blueflame1929/Mini-PCIe-Kineis-KIM1/Hardware/PCB/IMP-00008-X01-EC-TOP-IL1.pdf

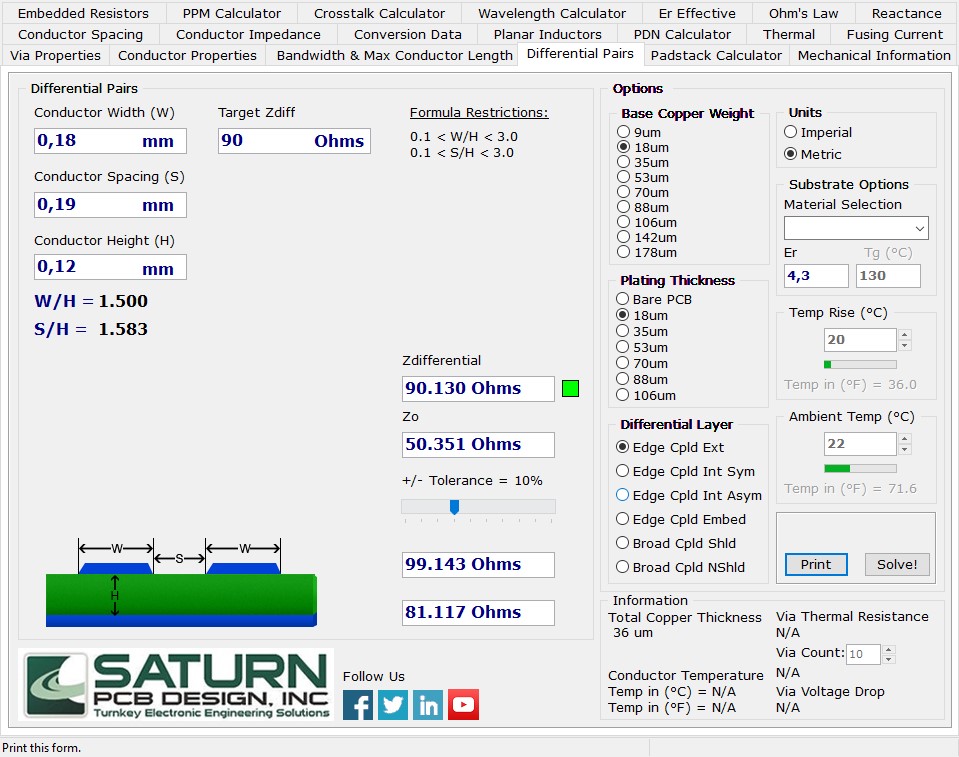
[picture p3: page 1]
