blueflame1929/Mini-PCIe-Kineis-KIM1/Hardware/PCB/IMP-00008-X01-MS-TOP-IL1.pdf

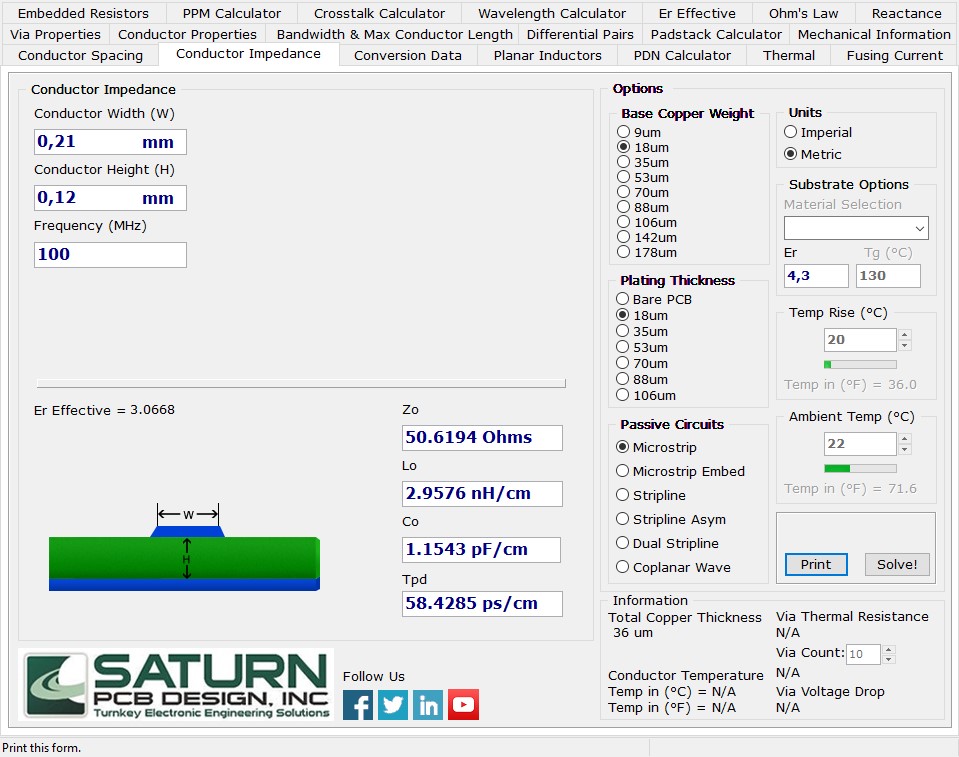
[picture p4: page 1]
