blueflame1929/Mini-PCIe-Kineis-KIM1/Hardware/ASY/B3D-00008-X01.png

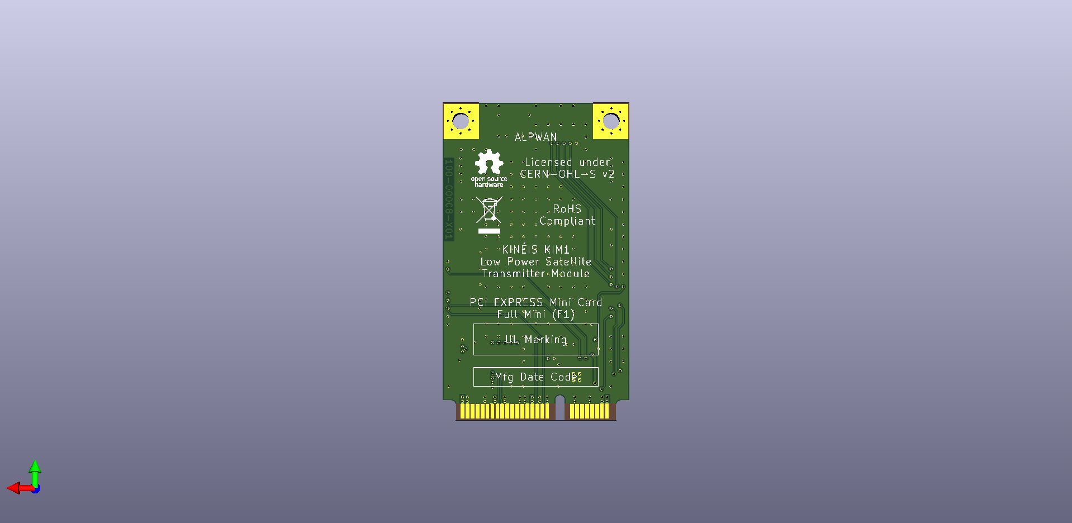
Hardware/ASY/B3D-00008-X01.png
