blueflame1929/Mini-PCIe-Kineis-KIM1/Hardware/PCB/MDD-00008-X01.pdf

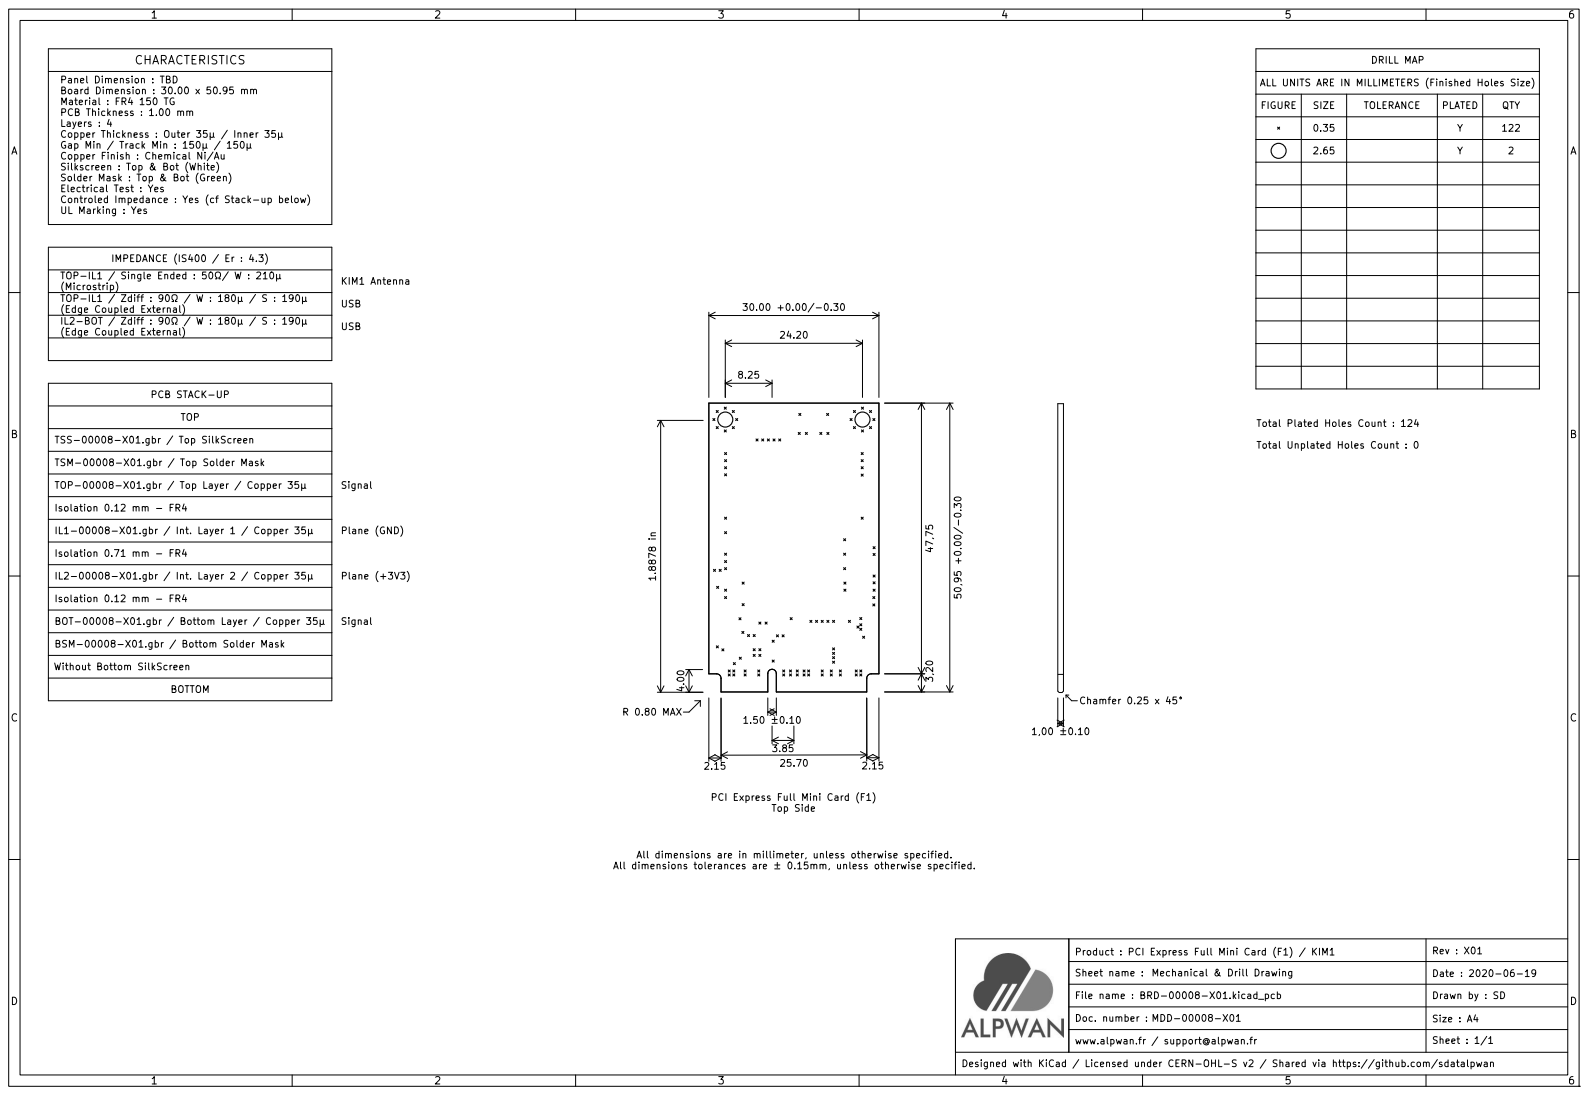
[picture p7: page 1]

IMPEDANCE (IS400 / Er : 4.3) Panel Dimension : TBD
Board Dimension : 30.00 x 50.95 mm
Material : FR4 150 TG
PCB Thickness : 1.00 mm
Layers : 4 Copper Thickness : Outer 35µ / Inner 35µ Gap Min / Track Min : 150µ / 150µ Copper Finish : Chemical Ni/Au Silkscreen : Top & Bot (White) Solder Mask : Top & Bot (Green) Electrical Test : Yes Controled Impedance : Yes (cf Stack-up below) UL Marking : Yes

TOP-IL1 / Single Ended : 50/ W : 210µ
Signal KIM1 Antenna USB TOP-IL1 / Zdiff : 90 / W : 180µ / S : 190µ

IL1-00008-X01.gbr / Int. Layer 1 / Copper 35µ PCB STACK-UP BSM-00008-X01.gbr / Bottom Solder Mask TOP

Isolation 0.12 mm - FR4 TSS-00008-X01.gbr / Top SilkScreen

Isolation 0.71 mm - FR4 TSM-00008-X01.gbr / Top Solder Mask

TOP-00008-X01.gbr / Top Layer / Copper 35µ Without Bottom SilkScreen

IL2-00008-X01.gbr / Int. Layer 2 / Copper 35µ

BOT-00008-X01.gbr / Bottom Layer / Copper 35µ

Rev : X01 Size : A4 Sheet : 1/1 Product : PCI Express Full Mini Card (F1) / KIM1 Sheet name : All dimensions are in millimeter, unless otherwise specified. All dimensions tolerances are ± 0.15mm, unless otherwise specified. PCI Express Full Mini Card (F1) Top Side

MDD-00008-X01 Mechanical & Drill Drawing
