blueflame1929/Mini-PCIe-Kineis-KIM1/Hardware/SCH/SCH-00008-X01.pdf

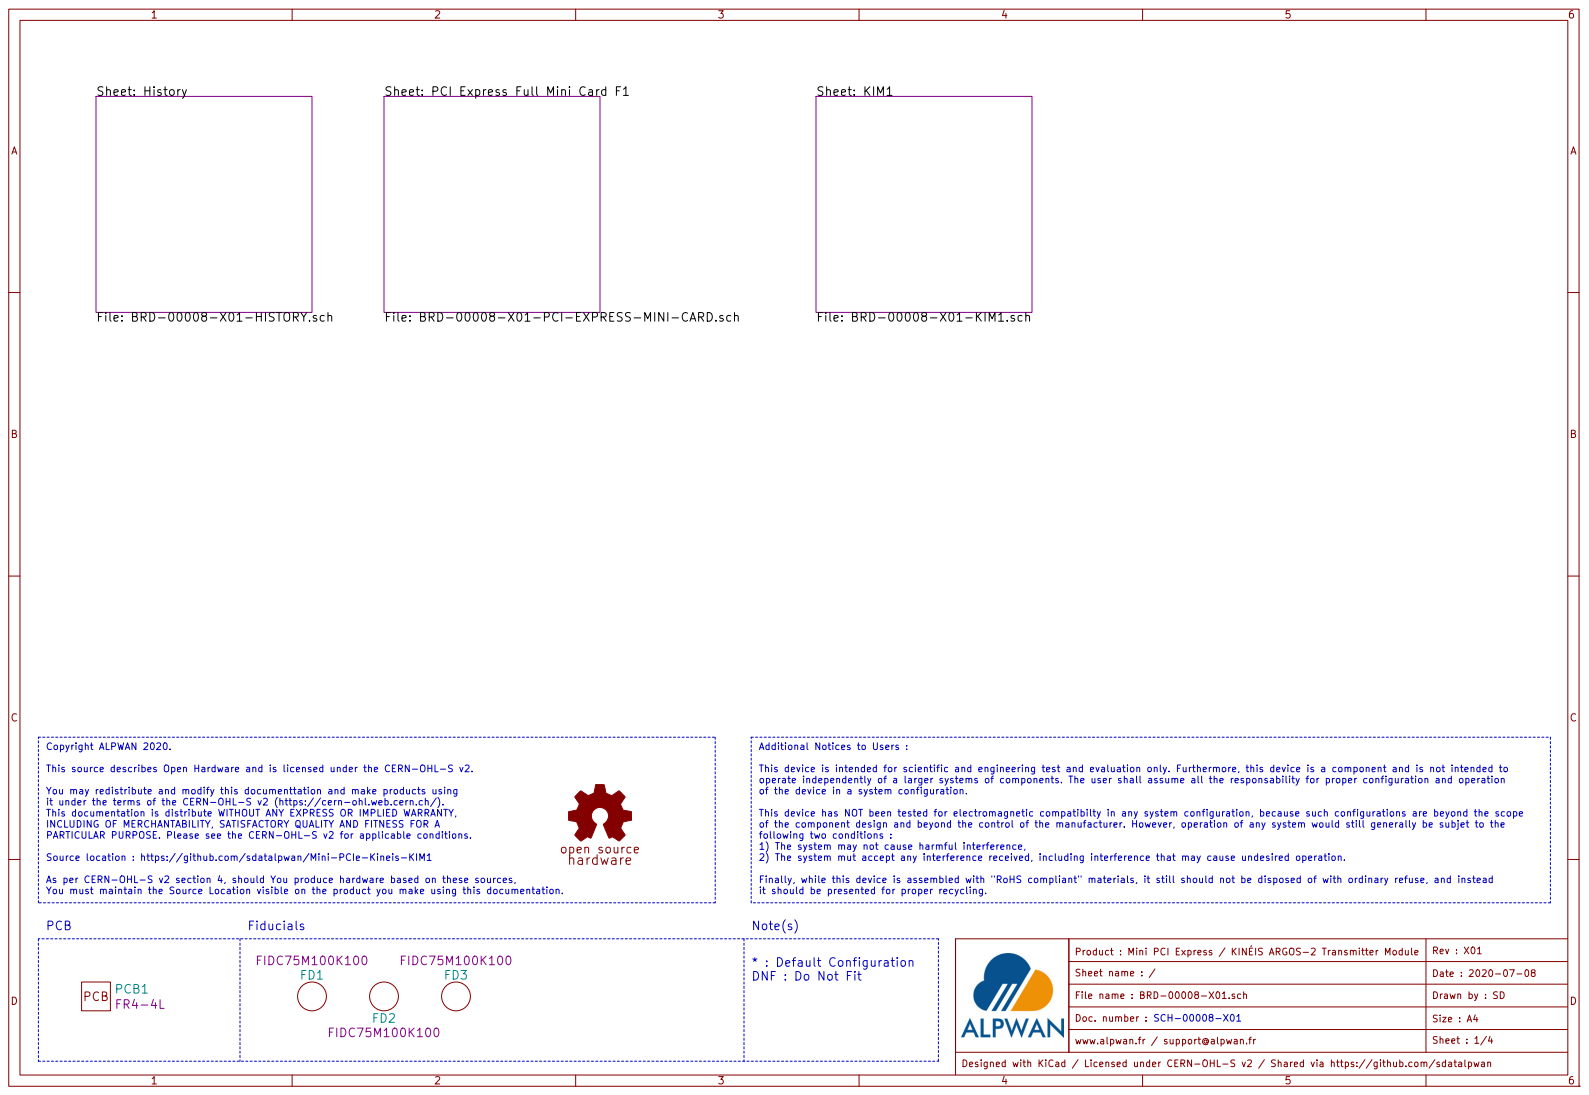
[picture p8: page 1]

Sheet: PCI Express Full Mini Card F1

Sheet: KIM1 File: BRD-00008-X01-KIM1.sch hardware

File: BRD-00008-X01-HISTORY.sch

File: BRD-00008-X01-PCI-EXPRESS-MINI-CARD.sch

Copyright ALPWAN 2020. This source describes Open Hardware and is licensed under the CERN-OHL-S v2. You may redistribute and modify this documenttation and make products using

of the device in a system configuration. This device has NOT been tested for electromagnetic compatibilty in any system configuration, because such configurations are beyond the scope

it under the terms of the CERN-OHL-S v2 (https://cern-ohl.web.cern.ch/). This documentation is distribute WITHOUT ANY EXPRESS OR IMPLIED WARRANTY,

INCLUDING OF MERCHANTABILITY, SATISFACTORY QUALITY AND FITNESS FOR A

of the component design and beyond the control of the manufacturer. However, operation of any system would still generally be subjet to the
following two conditions : 1) The system may not cause harmful interference, 2) The system mut accept any interference received, including interference that may cause undesired operation. Finally, while this device is assembled with "RoHS compliant" materials, it still should not be disposed of with ordinary refuse, and instead

* : Default Configuration DNF : Do Not Fit Fiducials

Rev : X01 Size : A4 Sheet : 1/4 Product : Mini PCI Express / KINÉIS ARGOS-2 Transmitter Module Sheet name : /

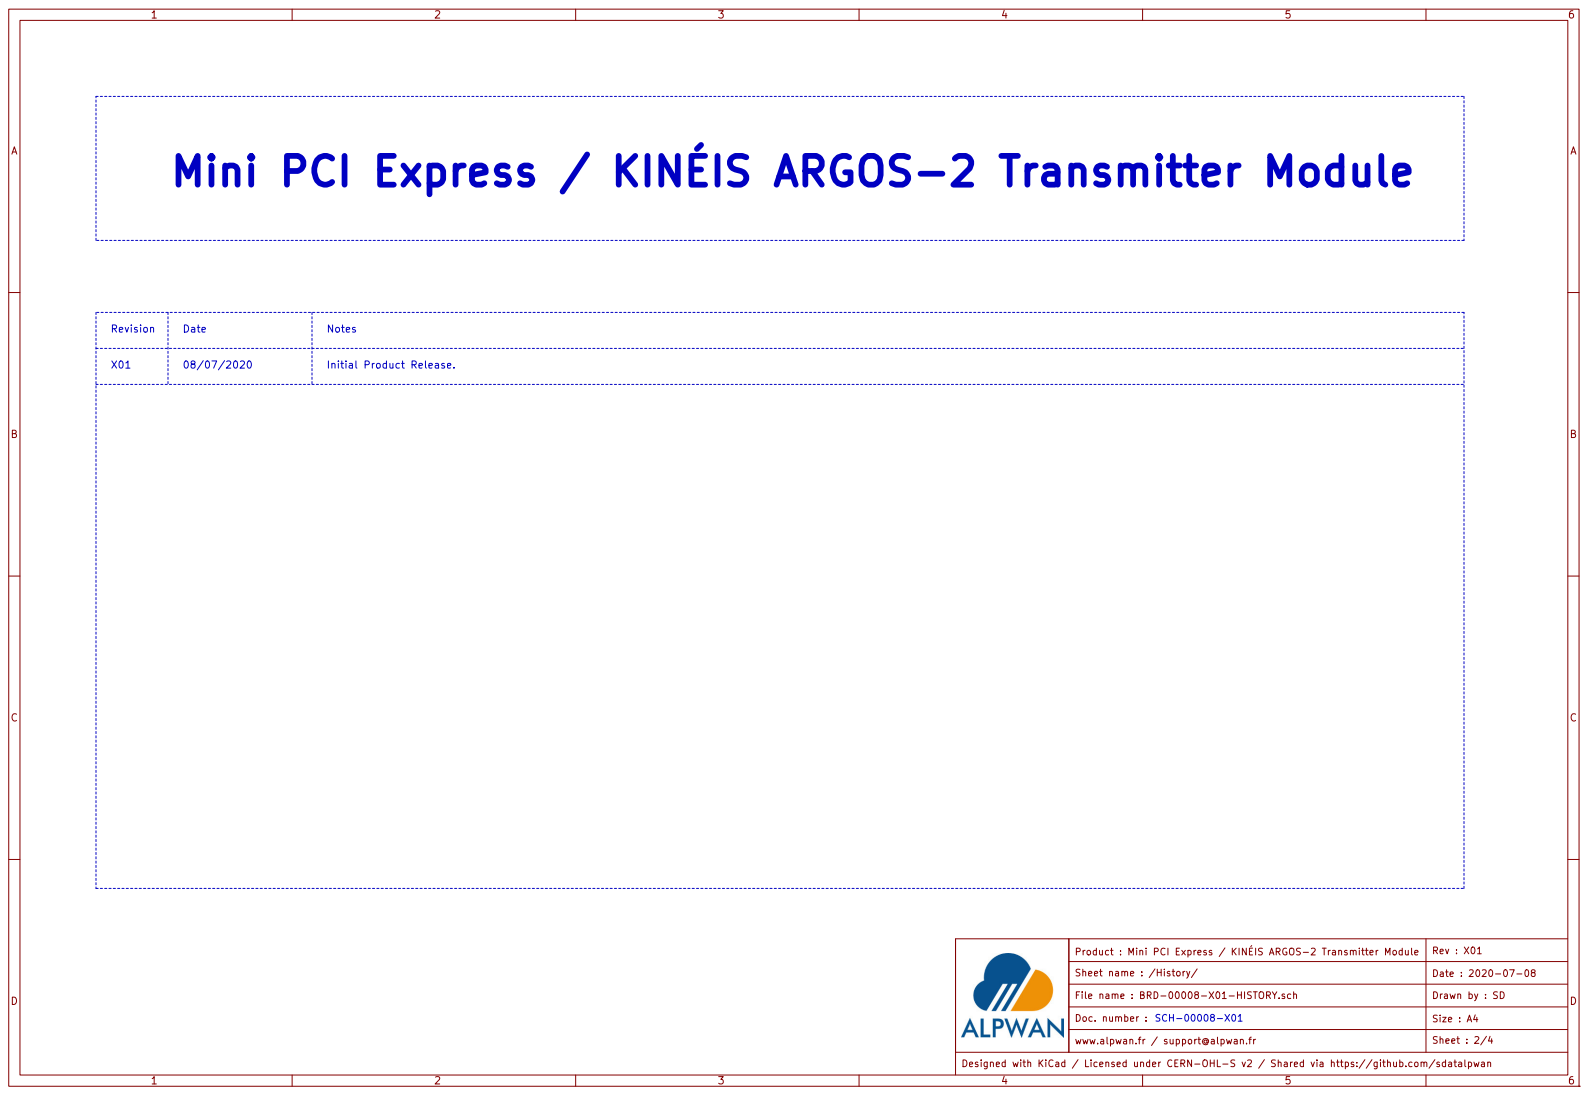
[picture p9: page 2]

Rev : X01 Size : A4 Sheet : 2/4 Product : Mini PCI Express / KINÉIS ARGOS-2 Transmitter Module Sheet name : /History/ Mini PCI Express / KINÉIS ARGOS-2 Transmitter Module

Revision | Date X01 08/07/2020 | Notes

Initial Product Release.

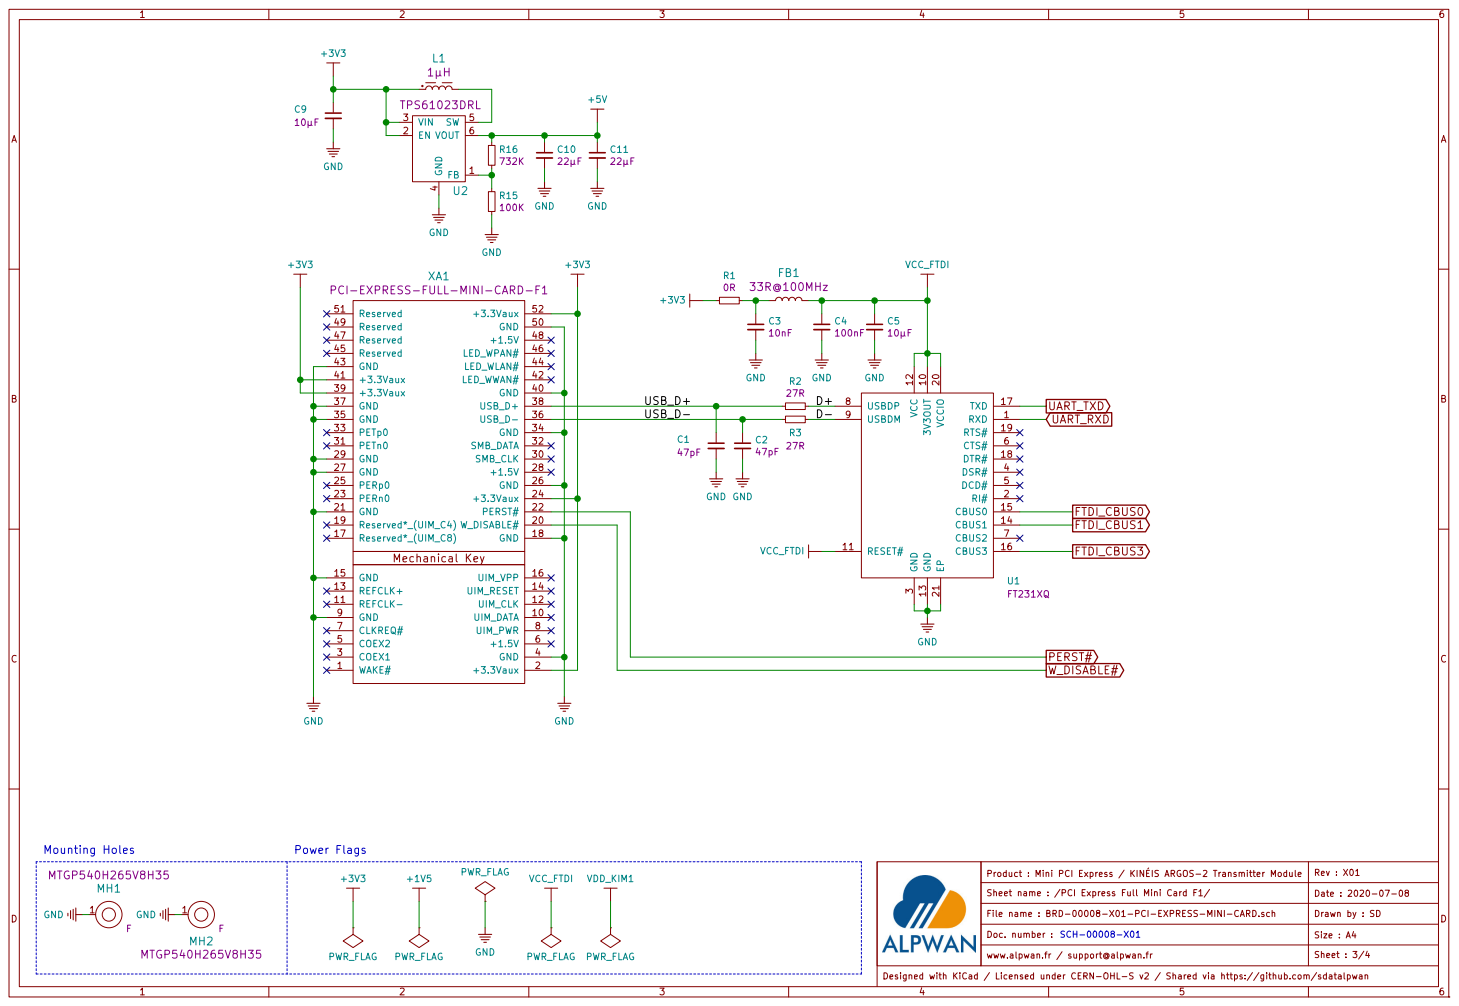
[picture p10: page 3]

4 SW 5 VOUT 6 U2 TPS61023DRL GND GND

3 DSR# 4 DCD# 5 CTS# 6 CBUS2 7 USBDP 8 USBDM 9 U1FT231XQ

Rev : X01 Size : A4 Sheet : 3/4 Product : Mini PCI Express / KINÉIS ARGOS-2 Transmitter Module Sheet name : /PCI Express Full Mini Card F1/ PWR_FLAG

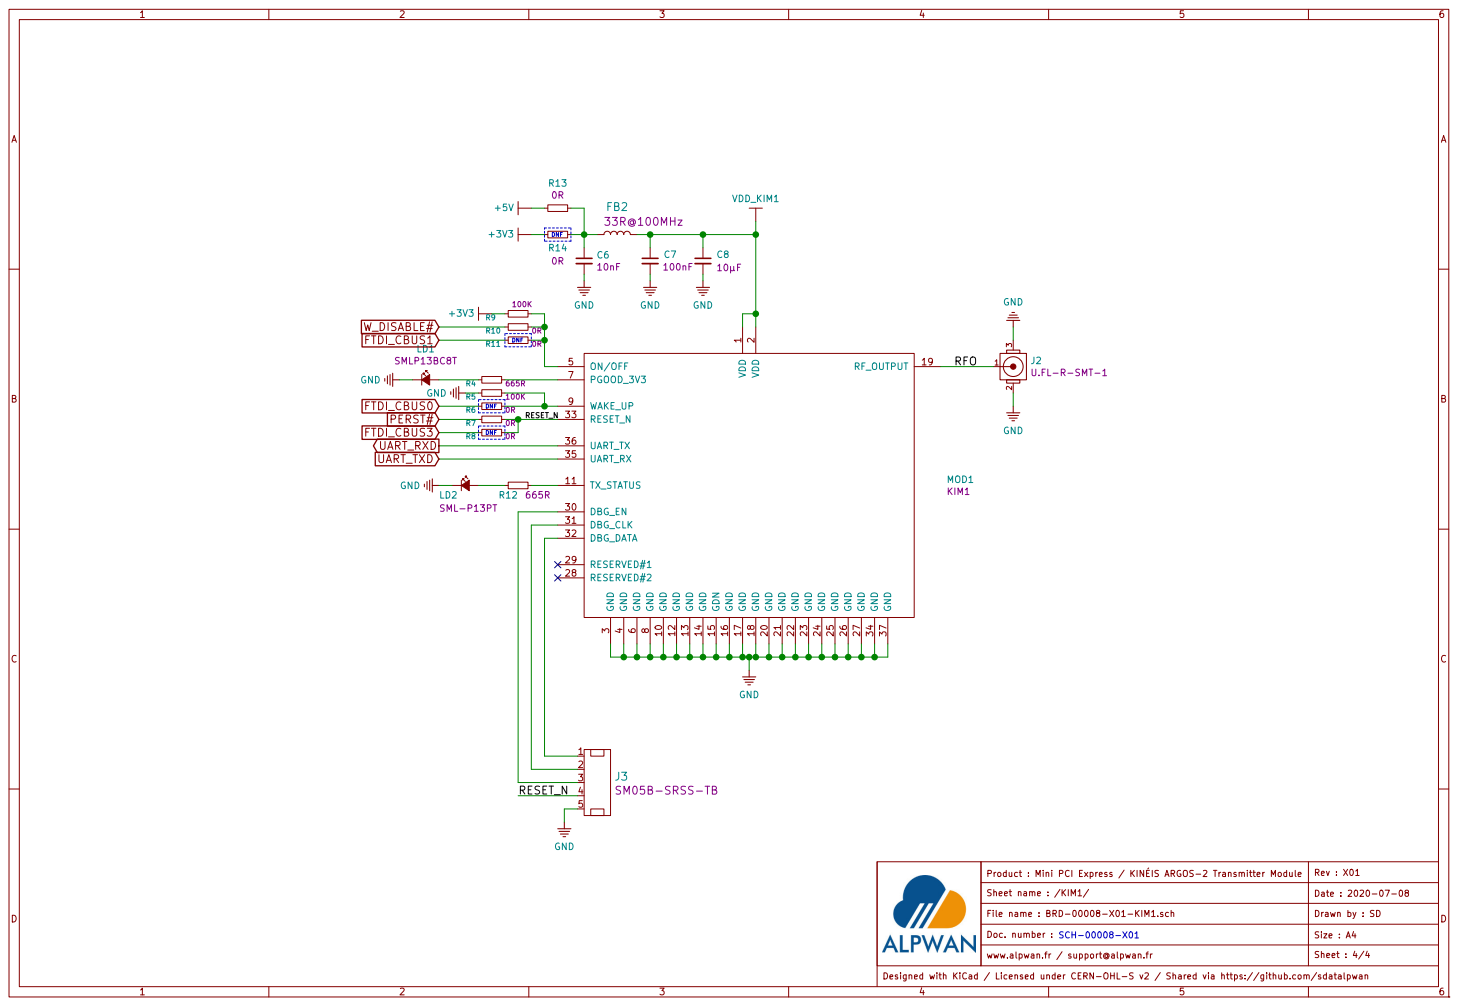
[picture p11: page 4]

1 GND 10 TX_STATUS 11 GND 12 GND 13 GND 14 GDN 15 GND 16 GND 17 GND 18 RF_OUTPUT 19 VDD

2 GND 20 GND 21 GND 22 GND 23 GND 24 GND 25 GND 26 GND 27 RESERVED#2 28 RESERVED#1 29 GND

Rev : X01 Size : A4 Sheet : 4/4 Product : Mini PCI Express / KINÉIS ARGOS-2 Transmitter Module Sheet name : /KIM1/
