blueflame1929/Mini-PCIe-Kineis-KIM1/Hardware/PCB/IL2-00008-X01.pdf

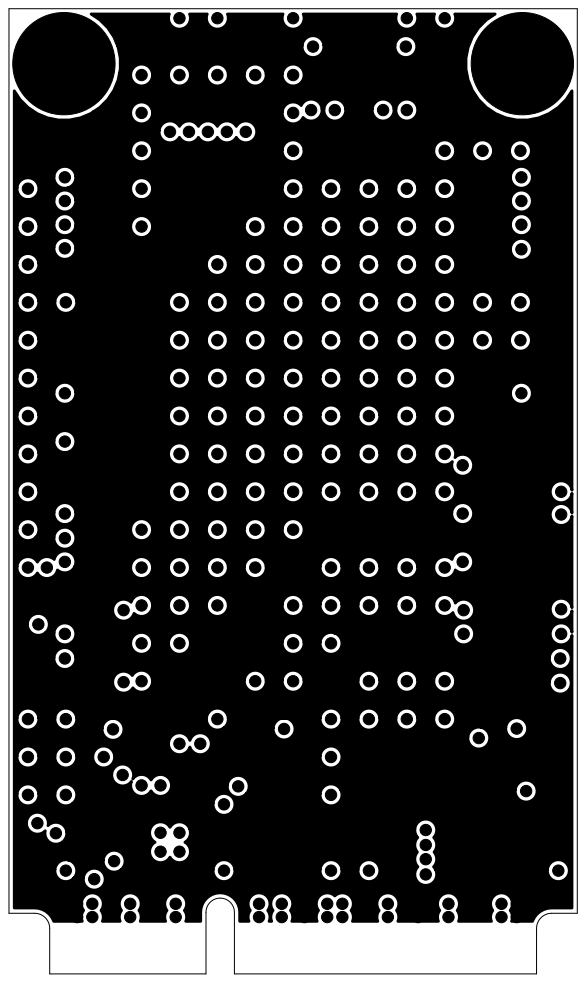
[picture p17: page 1]
