blueflame1929/Mini-PCIe-Kineis-KIM1/Hardware/PCB/TOP-00008-X01.pdf

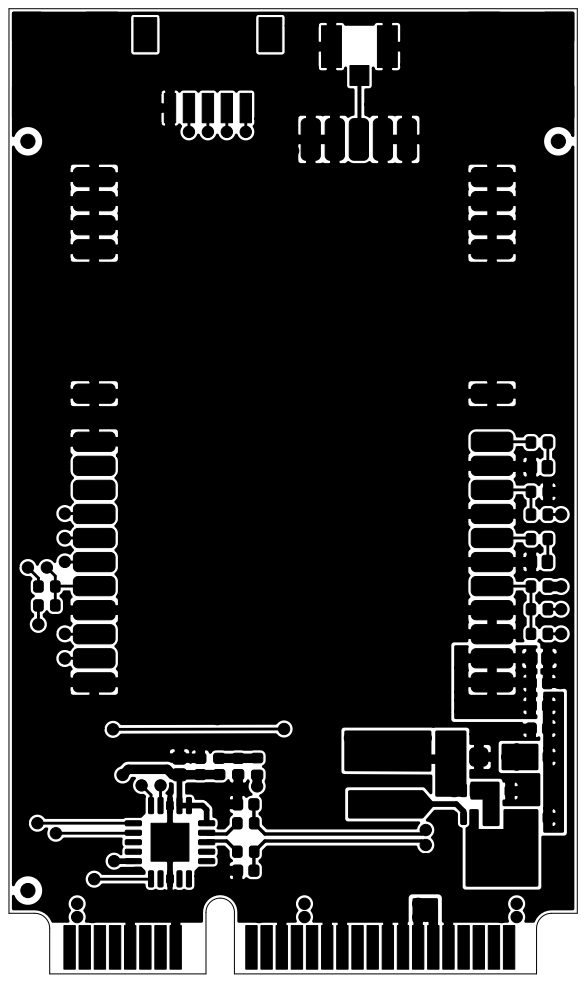
[picture p18: page 1]
