blueflame1929/Mini-PCIe-Kineis-KIM1/Hardware/PCB/TSM-00008-X01.pdf

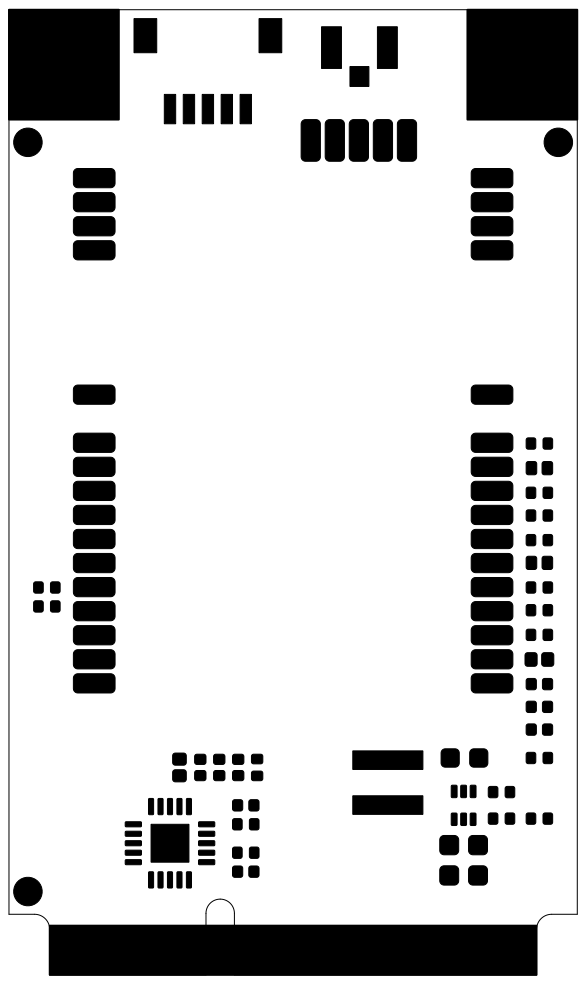
[picture p19: page 1]
