blueflame1929/Mini-PCIe-Kineis-KIM1/Hardware/PCB/TSS-00008-X01.pdf

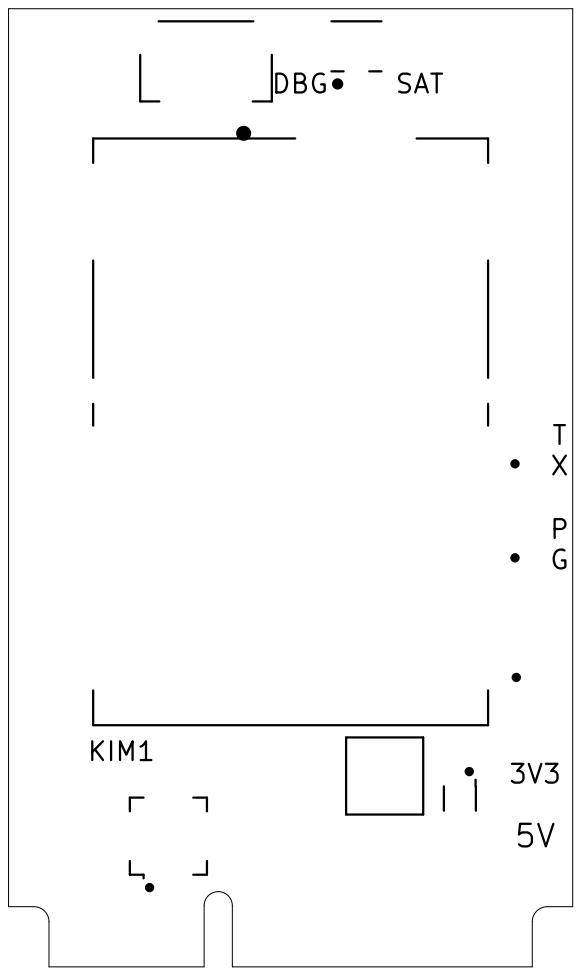
[picture p20: page 1]
